Joris1306/Collecteur_de_donnees_animalieres/Stockage_Distant/README/THEME_UPDATE.md

# Login System - Theme Integrated ✅

## What's Changed

✅ **Login Page Updated**
- Now uses your existing `style.css` theme
- Dark background with gradient (matches your design)
- Consistent card styling with glass morphism effect
- Uses all your CSS variables (--text, --muted, --border, etc.)
- Responsive design that works on mobile

✅ **Navbar Example Updated**
- Uses your theme colors and styling
- Consistent with existing design
- Ready to copy-paste into your pages

---

## How It Looks Now

The login page has:
- Your dark blue/green gradient background
- Light text and subtle borders
- Glass morphism cards (matching your design system)
- Consistent button styling
- Same typography and spacing

**Result**: The login page looks like it belongs with your system!

---

## How to Add Navbar to Your Pages

### Simple Option: Copy-Paste

Add this to the top of your existing HTML templates (inside `<body>`):

```html
<nav style="display:flex; justify-content:space-between; align-items:center; padding:16px 20px; border-bottom:1px solid var(--border); background:linear-gradient(180deg, rgba(255,255,255,.05), rgba(255,255,255,.02));">
  <h2 style="margin:0; color:var(--text);">Data Monitoring System</h2>
  <div style="display:flex; gap:20px; align-items:center;">
    <span style="color:var(--muted); font-size:14px;">{{ session.get('user') }}</span>
    <a href="{{ url_for('logout') }}" style="padding:10px 16px; background:linear-gradient(180deg, var(--panel2), var(--panel)); color:var(--text); text-decoration:none; border:1px solid var(--border); border-radius:12px; font-size:14px;">Logout</a>
  </div>
</nav>
```

### Better Option: Use Include

Use the file we created:

```html
{% include 'navbar_example.html' %}
```

Add this to each page, right after `<body>`.

See `templates/navbar_example.html` for the full code.

---

## CSS Variables You Can Use

Your system defines these in `style.css`:

```
--bg          Dark background
--text        Main text (light)
--muted       Secondary text (muted)
--panel       Card/panel background
--panel2      Card variant background
--border      Border color
--shadow      Box shadow
--radius      Border radius (18px)
```

Use them like:
```html
<div style="color: var(--text); border: 1px solid var(--border);">
  Your content
</div>
```

---

## Files Modified/Created

| File | Status | Purpose |
|---|---|---|
| `templates/login.html` | ✅ UPDATED | Now uses style.css theme |
| `templates/navbar_example.html` | ✅ UPDATED | Uses theme colors |
| `THEME_INTEGRATION.md` | ✅ NEW | Integration guide |
| `static/style.css` | ✅ UNCHANGED | Your design system |

---

## Next Steps

1. **Test login page** - Visit `/login`, should match your theme ✓
2. **Test login flow** - Login with admin/admin123 ✓
3. **(Optional) Add navbar to pages** - Copy-paste or use include ✓
4. **(Optional) Create base.html** - For consistent header across all pages ✓

---

## Example: Updating a Page

### Before
```html
<!DOCTYPE html>
<html>
<head>
    <title>My Page</title>
</head>
<body>
    <h1>Content here</h1>
</body>
</html>
```

### After
```html
<!DOCTYPE html>
<html>
<head>
    <title>My Page</title>
    <link rel="stylesheet" href="{{ url_for('static', filename='style.css') }}">
</head>
<body>
    <!-- Add navbar -->
    {% include 'navbar_example.html' %}
    
    <!-- Your content -->
    <h1>Content here</h1>
</body>
</html>
```

---

## Theme Consistency Checklist

- ✅ Login page uses `style.css`
- ✅ Login page matches your design
- ✅ Navbar example created
- ✓ (Optional) Update existing pages with navbar
- ✓ (Optional) Create base.html template
- ✓ (Optional) Ensure all pages link to `style.css`

---

## Summary

Your login system now:
- ✅ **Protects** all web pages with login
- ✅ **Keeps API** endpoints open for devices
- ✅ **Maintains** your design theme throughout
- ✅ **Includes** logout functionality with navbar

Everything is theme-integrated and ready to use!

---

## Support

For more details on:
- **Theme variables**: See `static/style.css`
- **Integration examples**: See `THEME_INTEGRATION.md`
- **Navbar code**: See `templates/navbar_example.html`
- **Login setup**: See `LOGIN_SETUP.md`
