Joris1306/Collecteur_de_donnees_animalieres/Rapport/CDC_PTRANS_CollecteurDonneesAnimalieres.pdf

# Cahier Des Charges

# Nom du projet : Collecteurs de données animalières

Version du document :

Finale

Date du document :

19 / 1 / 2026

Client :

Xavier Leprevost - élu de la mairie de Saint-Mars-du-Désert

Auteurs :

Davy Clark
Ewen Le Callet
Joris Menard
Jules Noumba
Nolan Buchet
Xueying Xu

Janvier 2026

## Table des matières

Page 2 sur 31

## Table des figures

II.1 | Bête à corne | | 7
II.2 | Décomposition en bloc fonctionnel principale | | 8
II.3 | Décomposition en blocs fonctionnels principaux et optionnels | | 9
II.4 | Diagramme des work package principaux (macro) | 10
II.5 | Diagramme Zoom sur le work-package principal numéro 1 "Acquisition des
données ou piège caméra" | 11

II.6 Diagramme Zoom sur le work-package principal numéro 2 "Réception, stockage
et exploitation des données" | 12
VII.1 Gantt des livrables de négociation et de suivi d’avancement du projet | 22

Page 3 sur 31

## Liste des tableaux

I.1 | Informations des intervenants | | 5
I.2 | Informations sur l’équipe de projet | | 6
II.2 | Détection de mouvement animalier | 13
II.4 | Prise de vue automatique | 14
II.6 | Stockage tampon pour transmission vers stockage distant | 15
II.8 | Autonomie énergétique | 16
II.10 Transmission des données | 17
VI.2 Tableau des risques du projet | 21
VIII.2 Signature des parties intervenant dans le projet | 25
XI.4 Comparaison des différentes technologies de transmission possibles | 28
XI.5 Comparaison des modules caméras | 29
XI.6 Comparaison des microcontrôleurs | 30
XI.7 Comparaison des microcontrôleurs (suite) | 31

Page 4 sur 31

# I Retranscription du besoin client

## 1 Contexte

La mairie de Saint-Mars-du-Désert est une collectivité territoriale dynamique et innovante, engagée dans une démarche de transition écologique et sociétale.

Dans ce cadre, la commune souhaite renforcer ses connaissances sur la faune locale en mettant en place un dispositif de surveillance et d’observation automatisée. Ce projet s’inscrit dans une démarche plus large de constitution de l’Atlas de la Biodiversité Communale (ABC), outil essentiel pour inventorier, comprendre et valoriser la richesse écologique du territoire.

Il s’intègre également dans un projet global porté par la municipalité et ses partenaires associatifs, visant au rachat et à la préservation de terrains naturels afin d’en assurer l’étude scientifique, la conservation et la valorisation écologique. Dans ce contexte, le dispositif envisagé pourra constituer un outil d’aide à la décision et un élément de preuve scientifique permettant de documenter la présence et l’évolution des espèces sur ces espaces protégés.

Le système aura pour objectif de capturer des photographies d’espèces animales présentes sur la commune. Dès leur acquisition, ces images seront transmises sans fil à un stockage distant afin d’être analysées par les services municipaux ainsi que par les partenaires scientifiques et associatifs.

## 2 Parties prenantes

Dans le cadre de ce projet, l’entité ayant le rôle de Maîtrise d’ouvrage (MOA)¹
sera la mairie de
Saint-Mars-du-Désert. L’interlocuteur ayant pour objectif de représenter la mairie dans ce projet sera
M. Xavier LEPREVOST, élu à la mairie de Saint-Mars-du-Désert.
QUI | RÔLE | MAIL | MOBILE
LEPREVOST Xavier | Client | Xavier.leprevost@saintmarsdudesert.fr | +33 6 28 34 18 50

Table I.1 – Informations des intervenants

Page 5 sur 31

Un groupe de six étudiants occupera le rôle de Maîtrise d’œuvre (MOE)²
. Ce groupe est composé
de trois étudiants ayant fait un BUT en électronique et informatique, un étudiant ayant fait une prépa PEIP (cursus préparatoire visant à préparer les élèves au cycle ingénieur Polytech), une étudiante ayant fait une licence en génie électrique et un étudiant ayant fait une licence en génie électrique, spécialité AII (automatique et informatique industrielle).
QUI | RÔLE | MAIL | MOBILE
LE CALLET Ewen | Chef de projet | ewen.le-callet@etu.univ-nantes.fr | +33 6 95 15 93 30
NOUMBA Jules | Reponsable work package secondaire Détection mou-vement et capteur T° | jules.noumba@etu.univ-nantes.fr | +33 6 11 83 82 77
BUCHET Nolan | Responsable work package principal Acquisition don-nées ou Piege Camera et du work package secondaire Gestion des échanges don-nées et du microcontrôleur | nolan.buchet@etu.univ-nantes.fr | +33 6 83 68 16 46
XU Xueying | Responsable work package secondaire Module caméra | xueying.xu@etu.univ-nantes.fr | +33 7 82 67 76 72
CLARK Davy | Responsable work package principal Réception, sto-ckage et exploitation des données et du work package secondaire Stockage distant | davy.clark@etu.univ-nates.fr | +33 7 85 78 48 46
MENARD Joris | Responsable work package principal Transmission | joris.menard@etu.univ-nantes.fr | +33 6 71 61 61 96

Table I.2 – Informations sur l’équipe de projet

Le lien avec les partenaires scientifiques, associatifs et naturalistes sera assuré par la mairie, notamment par l’intermédiaire de Xavier Leprevost. Les données et photographies produites dans le cadre du projet seront mises à disposition de la mairie, qui pourra les transmettre aux partenaires concernés et au public selon les besoins.

Page 6 sur 31

# II Besoins fonctionnels

La bête à corne ci-dessous permet de mieux comprendre les fonctions principales du projet, parties prenantes et objectifs du projet.

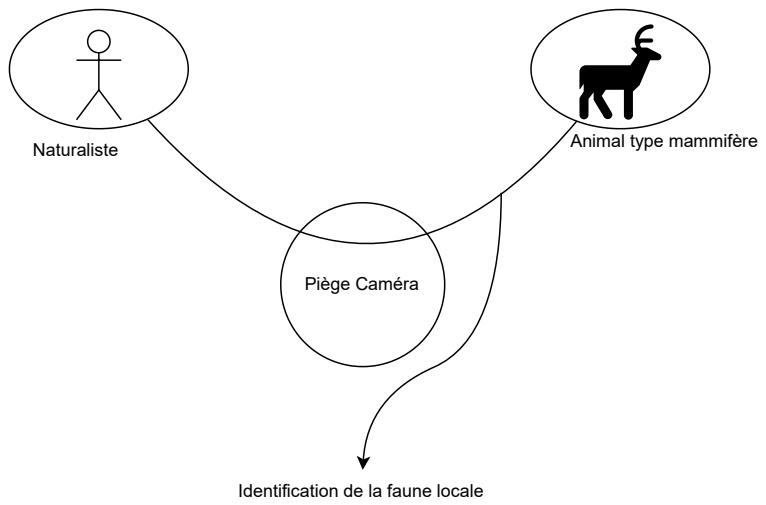
[picture p2: figure]
Piège Caméra; Naturaliste; Animal type mammifère; Identification de la faune locale

Figure II.1 – Bête à corne

Au regard des besoins exprimés par le client, le projet s’inscrit dans une démarche de preuve de concept (POC). L’objectif est de démontrer la faisabilité technique et opérationnelle d’un dispositif simplifié dans des conditions réelles, tout en maîtrisant les coûts et la complexité. Ce choix permet de concentrer les efforts sur un système fonctionnel, d’en valider les principes clés et de poser les bases pour d’éventuelles évolutions futures.

Pour garantir la simplicité et la fiabilité du dispositif, nous proposons de déployer un unique piège caméra, dont la collecte initiale se limitera à la prise de photos, à l’horodatage, la localisation GPS, l’humidité et la température. Cette approche vise à optimiser la gestion énergétique et à réduire la complexité fonctionnelle.

L’architecture du système sera conçue de manière modulaire afin de permettre l’intégration ultérieure d’autres types de données, sans remettre en cause l’ensemble de l’infrastructure.

Les données seront transmises vers un stockage distant dès leur acquisition, sans traitement préalable dans le piège caméra. Cette méthode permet d’éviter les contraintes liées à la gestion d’un stockage local volumineux et à la récupération fréquente des cartes SD, tout en facilitant la logistique et en assurant un accès centralisé aux données.

Enfin, les données seront structurées sous forme tabulaire dans le stockage distant et rendues accessibles via une interface web à accès restreind, afin de faciliter leur consultation, leur exportation et leur exploitation pour l’identification des espèces, conformément aux objectifs du projet.

Page 7 sur 31

Le système d’observation de la faune devra répondre à plusieurs besoins essentiels liés à sa mission principale : la collecte, la transmission et la mise à disposition des données sur les mammifères terrestres locales.

## 1 Fonctionnalités principales

— Détection de mouvement animalier : Le dispositif repose sur la détection automatique de mouvements dans son champ de vision. Il doit cependant être optimisé afin de se déclencher principalement lors de la détection d’un animal.

— Prise de vue automatique : une photo doit être prise dès qu’un mouvement est détecté.

— Enregistrement des images dans une mémoire tampon : les clichés capturés sont enregistrés dans une mémoire locale tampon avec leurs métadonnées (date, heure, température, humidité, position GPS) dans le but d’être transmis par la suite.

— Transmission des données : les données collectées doivent être envoyées vers un stockage distant.

— Autonomie énergétique : le système, basé sur une batterie, doit être capable de fonctionner de manière autonome grâce à une gestion optimisée de la consommation d’énergie. Il devra également intégrer un mécanisme de surveillance permettant de suivre en temps réel la capacité énergétique restante, afin d’anticiper les besoins de recharge ou de maintenance.

— Stockage distant : les données reçues par le piège caméra sont stockées dans un stockage distant dans le but d’être exploités.

— Interface utilisateur Web : une interface simple et ergonomique doit permettre la consultation des données (photos, localisation, informations environnementales, etc ...).

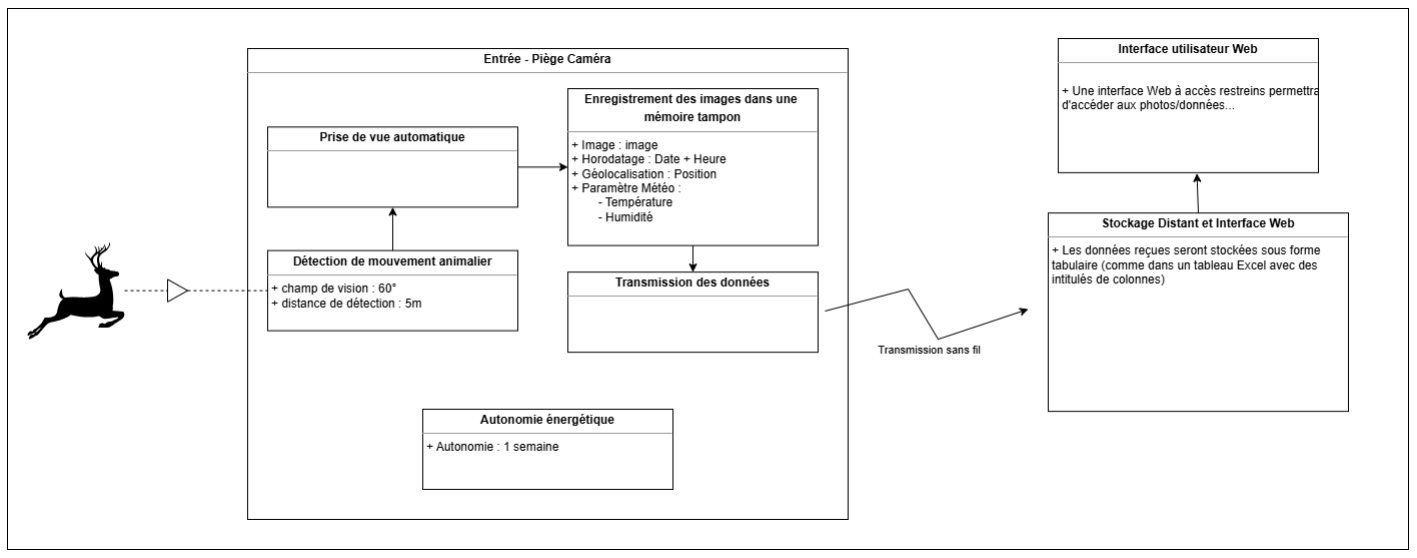
[picture p3: figure]

Figure II.2 – Décomposition en bloc fonctionnel principale

## 2 Fonctionnalités supplémentaires ou optionnelles

— Acquisitions de données environnementales supplémentaires : Ajouts d’autres mesures via divers moyen (pression atmosphérique, CO2, qualité de l’air, son, etc.).

Page 8 sur 31

— Traitement des images par IA : Réaliser une classification animalière sur les images du stockage distant et ajouter le résultat dans la base elle meme. Supression automatique des images non utiles (flous, humains etc...).

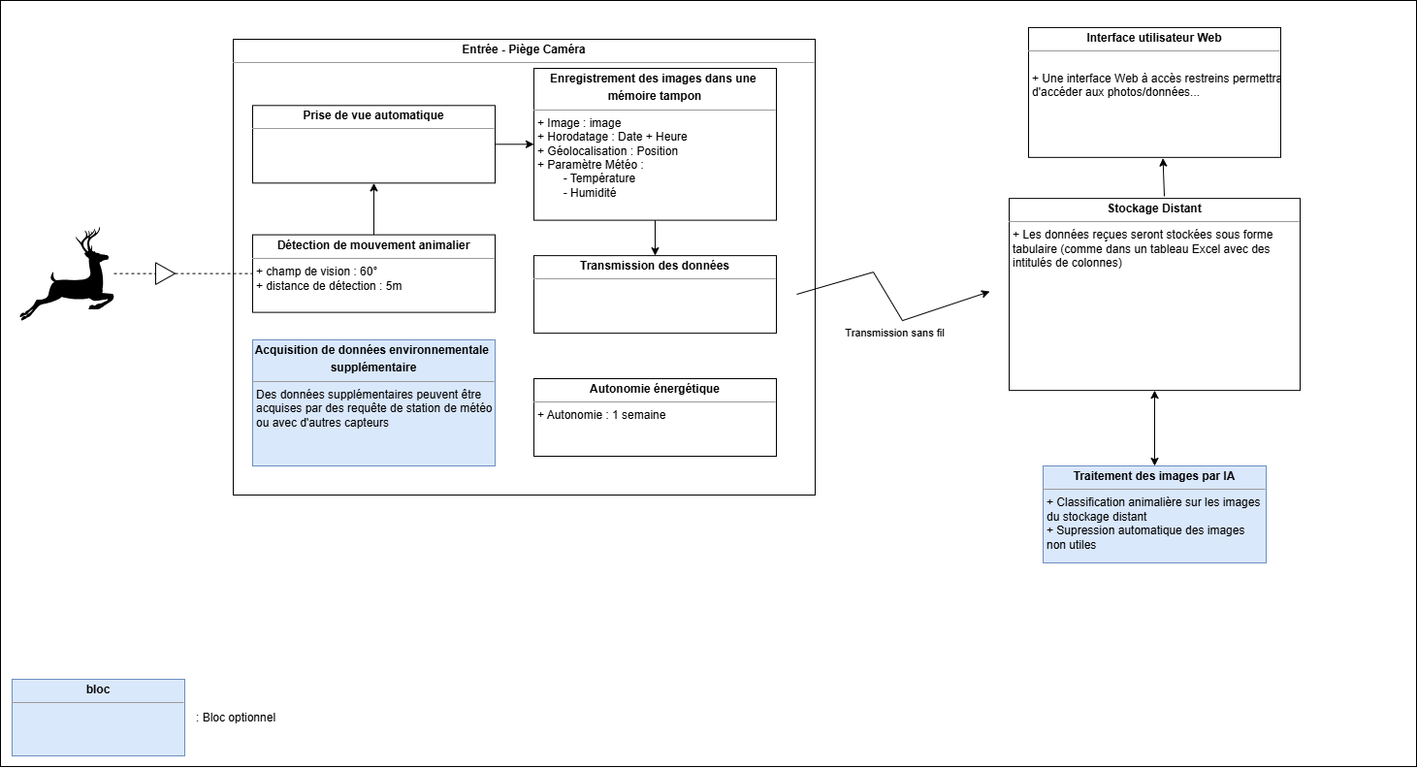
[picture p4: figure]

Figure II.3 – Décomposition en blocs fonctionnels principaux et optionnels

Page 9 sur 31

## 3 Répartition en Work packages

La répartition en WP du point de vu macro se décompose en deux WP principaux (acquisition des données ou piège caméra, puis réception, stockage et exploitation des données) ainsi qu’un WP bis dédié à la transmission. Cette décomposition se justifie par le fait que notre projet peut en réalité être scindé en deux sous-systèmes physiques distincts : le piège caméra et le stockage distant. La transmission constitue ainsi le lien entre ces deux entités.

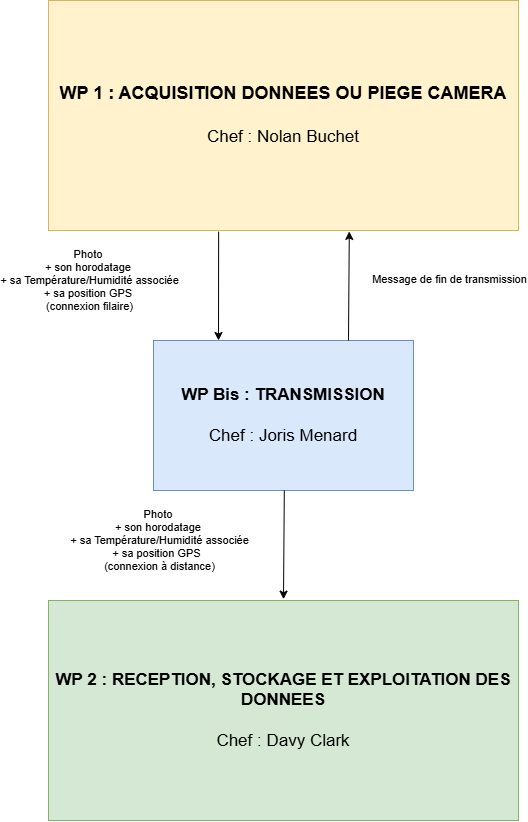
[picture p5: figure]

Figure II.4 – Diagramme des work package principaux (macro)

Décomposons dans un premier temps le WP principal numéro 1, intitulé « Acquisition des données ou piège caméra ». Ce WP est lui-même divisé en trois sous-WP :

— Détection de mouvement et capteurs de température et d’humidité : ce sous-WP a pour objectif le paramétrage du capteur PIR, la compréhension et l’optimisation de la surface de détection permettant le déclenchement des prises de vue. Il assure également l’acquisition des données environnementales associées aux images, à savoir la température et l’humidité.

Page 10 sur 31

— Gestion des échanges de données et du microcontrôleur : ce sous-WP garantit le transfert de l’ensemble des données acquises et la gestion du code embarqué dans le microcontrôleur, qui centralise et coordonne les différentes fonctions du système. Il inclut également la gestion énergétique du dispositif et l’horodatage.

— Caméra : ce sous-WP vise à s’assurer que la caméra réalise des prises de vue de jour comme de nuit avec une qualité suffisante pour l’exploitation des données.

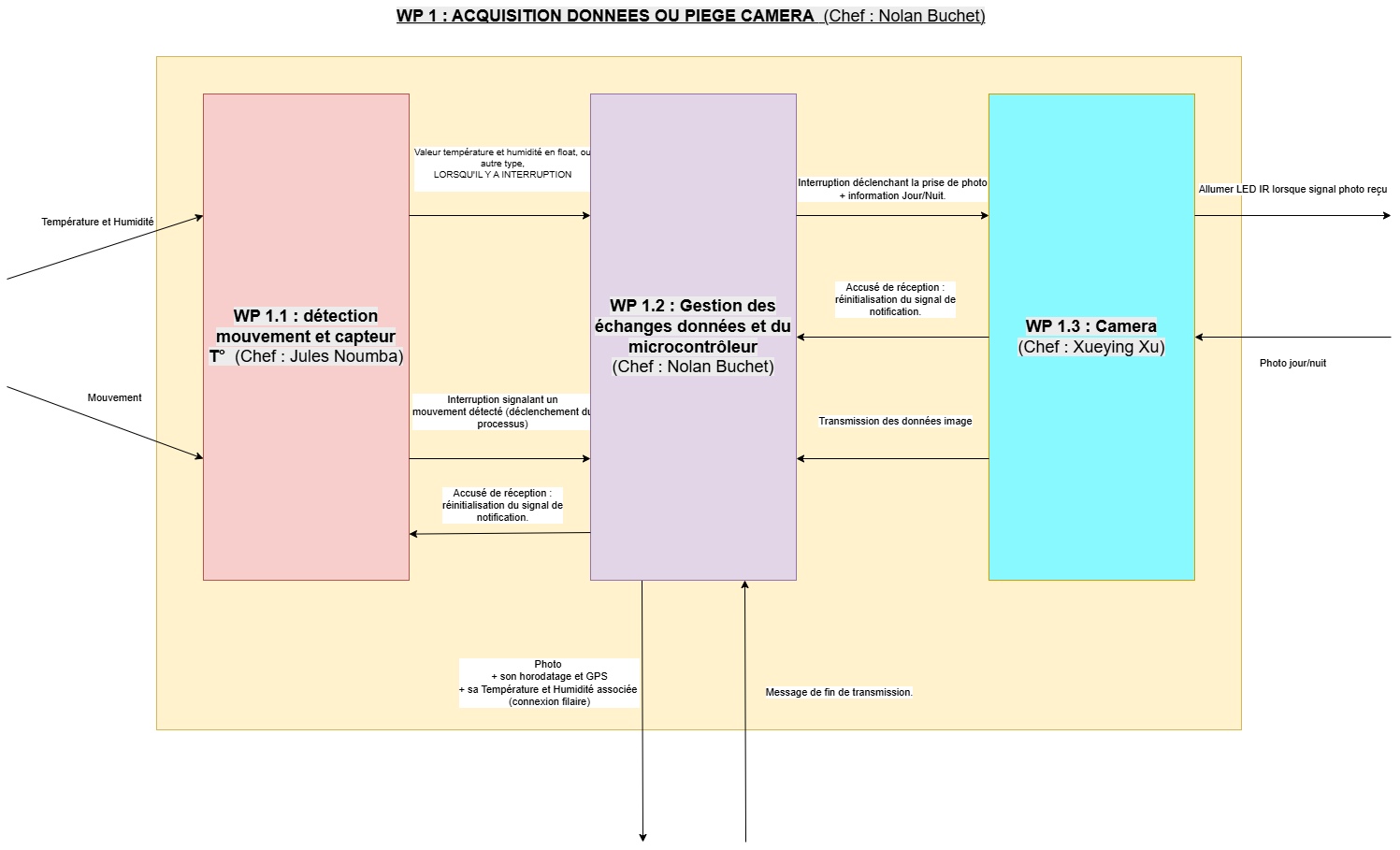
[picture p6: figure]

Figure II.5 – Diagramme Zoom sur le work-package principal numéro 1 "Acquisition des données ou piège caméra"

On se focalise désormais sur le WP principal numéro 2, intitulé « Réception, stockage et exploitation des données ». Ce WP se décompose en un sous-WP principal et deux sous-WP optionnels :

— Stockage distant : ce sous-WP assure la réception des données transmises à distance ainsi que leur stockage sous forme tabulaire sur une infrastructure distante.

— Interface utilisateur Web : ce sous-WP correspond au développement d’une interface web permettant de consulter les images acquises ainsi que les données associées (température, humidité, GPS, etc.). L’accès à cette interface est limité par une authentification.

— Traitement des images par IA – optionnel : ce sous-WP a pour objectif la récupération des images stockées à distance, leur traitement par un algorithme de classification d’animaux basé sur l’intelligence artificielle, puis le renvoi des résultats de la classification vers le stockage distant. On peut également implenter une supression automatique des images du stockage distant en fonction du résultat de l’algorithme IA.

Page 11 sur 31

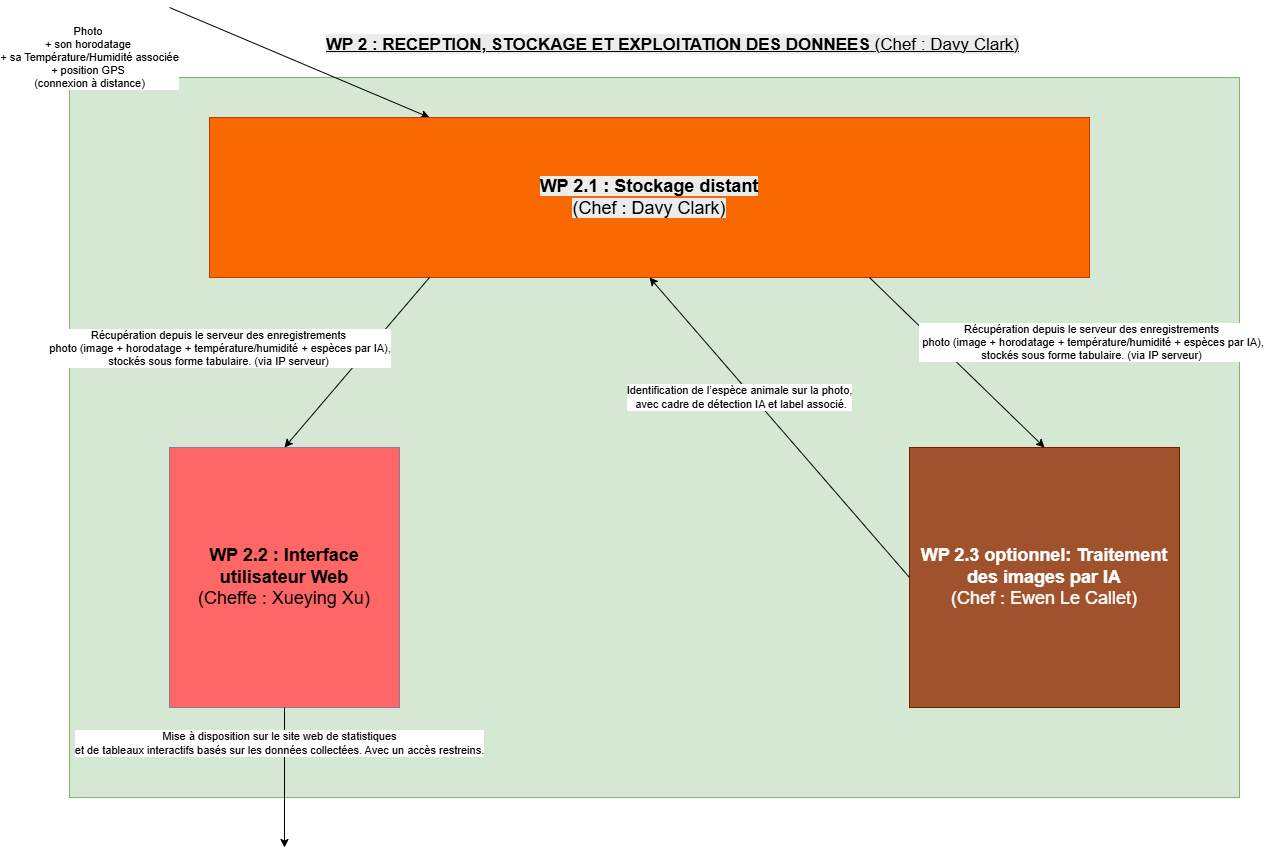
[picture p7: figure]

Figure II.6 – Diagramme Zoom sur le work-package principal numéro 2 "Réception, stockage et exploitation des données"

## 4 Spécifications techniques détaillées

Les tableaux suivants détaillent les spécifications techniques associées à chaque fonctionnalité principale. Pour chaque composant du système, sont précisés les paramètres de performance attendus, les données manipulées et les justifications techniques des choix retenus.

Cette formalisation permet d’établir des critères de validation clairs et d’assurer la cohérence de l’ensemble du système, tout en guidant les choix de conception et la sélection des composants.

Page 12 sur 31

Fonctionnalité | Données | Valeurs nomi-nales | Justification
Détection de présence | Zone de cou-verture | >2 m | Couvre la distance réaliste pour la plupart des animaux ciblés tout en limitant les déclenche-ments lointains dus au vent, branches ou objets ambiants ; réduit la consommation
| Angle de dé-tection | > 80 ° | Un angle minimal (>20°) ga-rantit qu’un animal traversant le champ proche est détecté sans multiplier les faux posi-tifs provoqués par une ouver-ture trop large.
Sensibilité du capteur | Temps de ré-action | ď 1 s après détection | Permet d’assurer la prise de vue de l’animal avant qu’il ne quitte la zone ; on peut viser ď1 s si le matériel et l’alimentation le permettent.
Adaptation environnementale | Conditions de fonctionne-ment | Jour / Nuit / Toutes saisons | mode jour et nuit, pour assurer couverture continue de la zone étudiée.
Température | Température de fonction-nement | -20 °C à +50 °C | Plage suffisante pour la majo-rité des zones tempérées ; pro-tège composants et batterie contre températures extrême
Etanchéité | | IP66 | Assure une protection totale contre la poussière et les pro-jections d’eau, adaptée à une installation extérieure perma-nente.

Table II.2 – Détection de mouvement animalier

Page 13 sur 31

Fonctionnalité | Données | Valeur No-minale | Justification
Distance | Portée maxi-male de photo exploitable | < 5 m | Une portée inférieure à 5 m permet de ga-rantir une bonne qualité d’image et une dé-tection efficace des animaux proches,
Champs | Champ de vi-sion de la ca-méra | > 20 ° | Un angle minimal (>20°) garantit qu’un animal traversant le champ proche est dé-tecté sans multiplier les faux positifs provo-qués par une ouverture trop large.
Enregistrement de l’image | Qualité de l’images | > 480p | Une résolution supérieure à 480p garantit une identification correcte des espèces tout en limitant la taille des fichiers pour un sto-ckage local efficace.
Nocturne | Prise de photo la nuit | Oui | La capture nocturne est indispensable pour un piège caméra, car de nombreuses espèces sont actives la nuit
Température | Témperature de fonction-nement | -15 °C / +50 °C | Plage suffisante pour la majorité des zones tempérées ; protège composants et batterie contre températures extrême
Rotation | Rotation de la caméra | Non | L’absence de rotation réduit la consomma-tion énergétique, le coût du dispositif et la complexité mécanique, tout en suffisant pour une zone de surveillance fixe.
Connectivité | Type de connectivité | Filaire | Une connexion filaire de la caméra sur le mi-crocontrolleur garantit la fiabilité du trans-fert.
Etanchéité | Norme Elec-tronique | IP66 | Assure une protection totale contre la pous-sière et les projections d’eau, adaptée à une installation extérieure permanente.
Type de flux | Flux interne | Photo | Le mode photo est prioritaire pour minimi-ser l’énergie consommée et maximiser la du-rée d’autonomie
Capture d’image | Format | JPEG/PNG | Ces formats standards assurent une compa-tibilité universelle et une bonne compression sans perte excessive de qualité.

Table II.4 – Prise de vue automatique

Page 14 sur 31

Fonctionnalité | Données | Valeurs nomi-nales | Justification
Enregistrement local tampon | Support de stockage | Mémoire interne (microSD 32 Go min.) | Une carte microSD est peu coûteuse, facilement remplaçable et offre une ca-pacité suffisante pour stocker plusieurs jours.
Sauvegarde auto-matique | Fréquence d’enregistre-ment | À chaque détection de mouvement | Cette logique d’enregistrement ga-rantit qu’aucun événement anima-lier n’est perdu tout en limitant la consommation mémoire.
Métadonnées as-sociées | Date et heure d’ac-quisition | Format ISO 8601 (AAAA-MM-JJ HH :MM :SS) | Le format ISO standardise les enregis-trements temporels, facilitant la syn-chronisation et le tri automatisé des fichiers.
| Température ambiante | ±1 °C de précision | précision suffisante pour les besoins terrain.
| Position GPS | Précision ď 5 m | Une précision inférieure à 5 m est suf-fisante pour localiser précisément la zone de capture
Gestion mémoire | Seuil d’alerte de satura-tion | 90 % d’utilisation de la capacité | Définir une alerte avant saturation permet d’éviter la perte de données
Effacement auto-matique | Politique de remplace-ment | Suppression des plus anciens fichiers lorsque transmis-sion effectuée | Assure la continuité du stockage sans intervention humaine

Table II.6 – Stockage tampon pour transmission vers stockage distant

Page 15 sur 31

Fonctionnalité | Données | Valeurs nominales | Justification
Source | Type de bat-terie | Li-ION | Les batteries Li-Ion offrent une haute densité énergétique, une bonne durée de vie, et sont facilement rechargeables, ce qui les rend idéales pour un dispositif autonome en extérieur.
Tension | | 3.7V | Tension standard pour les modules électro-niques basse consommation, assurant compa-tibilité avec la plupart des composants embar-qués.
Autonomie | Duré de fonctionne-ment | 1 semaine | Une autonomie d’une semaine garantit un fonctionnement prolongé sans intervention hu-maine
Gestion Energé-tique | Mode de veille | 30 s de dé-tections | Permet de réduire significativement la consom-mation lorsque le dispositif est inactif, tout en maintenant une réactivité satisfaisante à la dé-tection suivante.
Conso veille | | < 100 uA | Très faible consommation permettant d’écono-miser la batterie sur les longues périodes d’in-activité, essentielle pour un piège caméra sou-vent en veille.
Conso Activité | | < 1 W | Une faible consommation en activité prolonge la durée de fonctionnement global et limite les besoins de recharge fréquente.
Protection elec-trique | Sécurité | Surchage | La protection contre la surcharge empêche toute détérioration de la batterie lors de la re-charge, augmentant la sécurité et la durée de vie du système.
| Surtension | | La protection contre la surtension protège les circuits électroniques contre les variations de tension, garantissant la fiabilité du dispositif.
Information | | Envoie une alerte concernant < 10 % | Une alerte de batterie faible permet d’anticiper la recharge ou le remplacement avant l’arrêt complet du système, évitant la perte de don-nées ou d’observations.
Plage de fonc-tionnement | Température de fonction-nement | -20 °C à +50 °C | Assure la fiabilité du système dans la plu-part des environnements naturels, incluant des conditions hivernales et estivales extrêmes.

Table II.8 – Autonomie énergétique

Page 16 sur 31

Fonctionnalité | Données | Valeurs no-minales | Justification
Type de commu-nication | 4G | Sans Fils | La communication sans fil permet un transfert automatique des données sans in-tervention manuelle, indispensable pour un système autonome déployé sur le terrain.
Donnée | | Image
| | Metadonnées
Stockage distant | Type de ser-veur | Serveur local | Un serveur local permet une liberté suffi-sante pour répondre de plusieurs manières différentes aux besoins.
Consomation | Mode de trans-mission | < 2 W | La consommation limitée à 2 W préserve l’autonomie énergétique du système lors des envois, particulièrement importants si la transmission est fréquente.
Condition d’en-voie | Declanchement | Envoie après Chaque cap-ture | L’envoi immédiat permet la mise à jour en temps réel des données dans le stockage distant, utile pour un suivi continu ou des alertes rapides.

Table II.10 – Transmission des données

Page 17 sur 31

# III Besoins non fonctionnels

En plus des fonctionnalités attendues, le système devra respecter plusieurs contraintes techniques et qualitatives :

— Fiabilité : le système doit fonctionner de manière continue dans des conditions extérieures variables (pluie, vent, variations de température).

— Robustesse : les composants matériels doivent être les plus résistants possibles aux intempéries et aux chocs.
— Évolutivité : l’architecture logicielle et matérielle doit permettre l’ajout de nouveaux capteurs ou modules sans modification majeure.

— Performance : la détection et la transmission doivent être sans perte d’informations.

— Energie et autonomie : Comme on peut le constater dans le tableau des spécifications cidessus, le système doit être conçu pour une faible consommation énergétique et disposer d’une autonomie suffisante afin d’assurer un fonctionnement prolongé. Une autonomie de 1 semaine a été définie afin de garantir la flexibilité du système et d’assurer sa continuité de fonctionnement.

Page 18 sur 31

# IV Évolution potentielle des besoins

Le système devra être conçu pour permettre des évolutions futures, tant sur le plan matériel que logiciel :

— Amélioration du traitement d’image : intégration d’algorithmes plus performants de reconnaissance d’espèces animales à l’aide de l’intelligence artificielle.

— Ouverture vers la participation citoyenne : intégration complète d’une application mobile et mise en place d’un système de validation des données saisies par les habitants.

— Interopérabilité : possibilité de connecter le système à d’autres bases de données environnementales régionales ou nationales.

— Extension du réseau de surveillance : déploiement de plusieurs caméras réparties sur un vaste périmètre afin d’assurer une couverture complète de la zone. Les données sont d’abord centralisées localement via un module de regroupement chargé de collecter les données des différentes caméras, puis transmises vers le serveur central.

Page 19 sur 31

# V Limites du projet

Ce projet vise exclusivement la prise d’informations (photo, GPS, horodatage, température, humidité) liés à l’identification d’animaux terrestres de taille significative (ex. mammifères sauvages). Afin d’assurer un cadrage clair du besoin, les limites suivantes sont définies

## 1 Fonctionnalités limitées à la détection et de la prise de vue

Bien que le système, basé sur la détection de mouvement, puisse être parasité par la détection d’humains, d’oiseaux ou d’autres éléments, son objectif principal reste la détection et la photographie d’animaux terrestres. Les insectes, oiseaux, petits rongeurs et tout animal de taille trop réduite ne sont pas pris en compte dans le cadre du projet. Le système ne réalise aucune capture vidéo, seules des photographies sont enregistrées par la caméra. Le projet se limite à un but d’identification d’espèces et non d’analyse du comportement.

## 2 Couverture géographique restreinte

Les tests et le déploiement initial sont réalisés exclusivement sur le territoire de Saint-Mars-du-Désert, dans le bois communal.

## 3 Conditions d’installation contrôlées

Le dispositif est destiné à être fixé sur un support solide (arbre, poteau, structure dédiée). Aucune installation dans l’eau ou dans des sols boueux instables n’est envisagée.

Page 20 sur 31

# VI Risques

Cette section présente les risques identifiés pour le projet, classés par catégorie. Pour chaque risque, nous indiquons la probabilité d’occurrence, la gravité et le niveau de risque, ainsi que les mesures préventives ou correctives proposées. L’objectif est d’anticiper les incidents potentiels et de définir des actions permettant de réduire leur impact sur le planning, le budget et la qualité des livrables.

Catégorie | Risque identifié | Probabilité | Gravité | Niveau de risque | Mesures pré-ventives / Correctives
Gestion de projet | Mauvaise réparti-tion des tâches | moyen | moyen | moyen | Fiche de suivi des tâches
Gestion de projet | Mauvaise com-munication avec le client | moyen | haut | haut | Communiquer régulièrement et précisément avec le client
Gestion de projet | Mauvaise com-munication entre les membres | faible | haut | moyen | Team building, baromètre d’at-mosphère de l’équipe
Gestion de projet | Prise de décisions | moyen | moyen | moyen | Répartition en Work Package Work Package (WP)³
Gestion de projet | Mécompréhension due à la barrière de la langue | moyen | moyen | moyen | Nommer per-sonnes chargées de la traduction et former duo
Gestion de projet | Manque d’impli-cation dû à la lar-geur du groupe | haut | moyen | moyen | Donner des tâches per-sonnalisés et responsabiliser l’équipe

Table VI.2 – Tableau des risques du projet

Page 21 sur 31

# VII Planning

Durant ce projet, plusieurs types de livrables seront remis au client, tel que les comptes-rendus de réunion, les soutenances, ou d’autres documents de suivi. Afin de clarifier certains points d’interrogation et de rendre compte de l’avancement du projet. Par ailleurs, il existe également les livrables produits, qui correspondent aux différentes composantes du produit à rendre tout au long de la phase de développement, ou au produit final lui-même à rendre à la fin du projet.

Le diagramme de Gantt ci-dessous permet de visualiser les livrables, tels que les réunions et les documents à remettre au client.

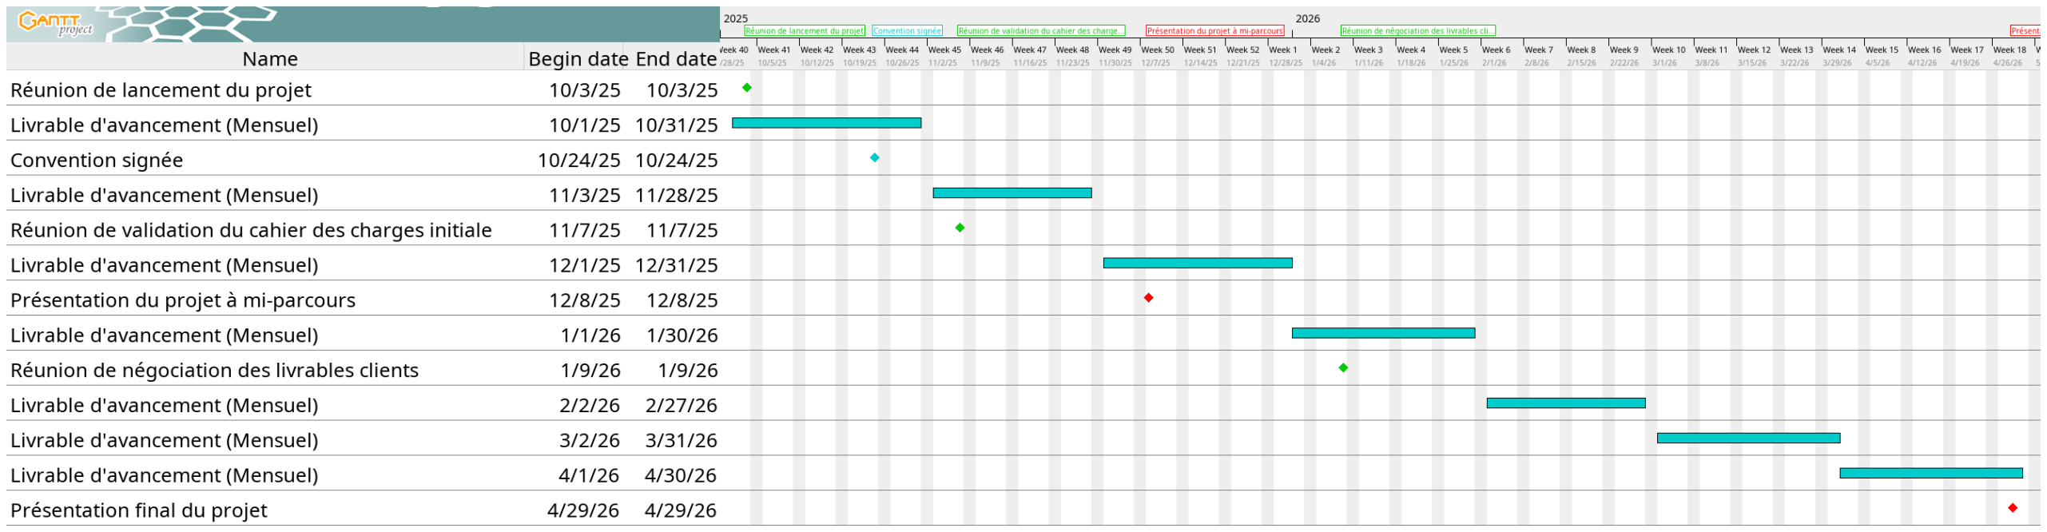
[picture p8: figure]

Figure VII.1 – Gantt des livrables de négociation et de suivi d’avancement du projet

Un court rapport mensuel sera remis au client afin de suivre l’avancement du projet. La fréquence de remise de ce rapport pourra évoluer au cours du projet selon les demandes du client.

Page 22 sur 31

# VIII Gestion de projet

## 1 Décomposition en work packages (WP)

Le projet est structuré en différents WP, permettant une répartition claire et cohérente des tâches entre les membres de l’équipe. Cette organisation facilite la gestion du projet, la responsabilisation de chaque collaborateur et le suivi de l’avancement des travaux.
D’un point de vue macro, le projet est décomposé en deux WP principaux et un WP bis. Cette décomposition repose sur l’architecture globale du système, qui peut être scindée en deux sous-systèmes physiques distincts : le piège caméra et le stockage distant. Le WP bis « Transmission » assure le lien fonctionnel entre ces deux entités.

### 1.1 Work packages principaux

WP1 – Acquisition des données ou piège caméra Ce WP regroupe l’ensemble des fonctionnalités liées au sous-système embarqué. Il comprend notamment l’acquisition des images et des données environnementales, ainsi que la gestion du matériel et de l’énergie. Il se décompose en plusieurs sous-WP :
— Détection de mouvement et capteurs environnementaux : paramétrage du capteur PIR, optimisation de la zone de détection et acquisition des données de température, d’humidité et autres métadonnées associées aux images.
— Gestion des échanges de données et du microcontrôleur : centralisation des données, gestion du code embarqué, horodatage et gestion énergétique du dispositif.
— Caméra : sélection et intégration du module caméra afin d’assurer des prises de vue de jour comme de nuit avec une qualité suffisante pour l’exploitation des données.

WP2 – Réception, stockage et exploitation des données Ce WP concerne le sous-système distant et le traitement des données transmises par le piège caméra. Il se décompose en 2 sous-WP principaux et un sous-WP optionnel :

— Stockage distant : ce sous-WP assure la réception des données transmises à distance ainsi que leur stockage structuré sous forme tabulaire sur une infrastructure distante.
— Interface utilisateur Web : ce sous-WP correspond au développement d’une interface web permettant de consulter les images acquises ainsi que les données associées (température, humidité, coordonnées GPS, etc.). L’accès à cette interface est limité par un mécanisme d’authentification afin de garantir la confidentialité des données.
— Traitement des images par IA – optionnel : ce sous-WP a pour objectif la récupération des images stockées à distance, leur traitement par un algorithme de classification d’animaux basé sur l’intelligence artificielle, puis le renvoi des résultats de la classification vers le stockage distant. Il pourra également intégrer une suppression automatique des images du stockage distant en fonction des résultats fournis par l’algorithme d’IA.

### 1.2 Work package bis – Transmission

Le WP bis « Transmission » est transverse aux deux WP principaux. Il a pour objectif d’assurer la communication sans fil entre le piège caméra et le stockage distant. Ce WP inclut le choix de la

Page 23 sur 31 technologie de communication, la fiabilité des échanges et la validation de la trame de données, ainsi que l’optimisation de la consommation énergétique liée à la transmission.

Page 24 sur 31

## 2 Signatures du projet

Date | et | signature | du
client

Date et signature du chef
de projet
Date | et | signature | des
coachs de projet

Table VIII.2 – Signature des parties intervenant dans le projet

Page 25 sur 31

# IX Démarche de transition écologique

Ce projet s’inscrit pleinement dans une démarche de transition écologique en soutenant la connaissance et la préservation de la biodiversité locale. Ce projet facilite la collecte d’images d’animaux sauvages pour alimenter l’atlas de la biodiversité communale et aider les experts à mieux inventorier la faune du territoire.

Page 26 sur 31

Page 27 sur 31

# XI Annexes

Afin de trouver la meilleur solution technique pour chaque work package du projet, un Benchmark⁴ à été mis en place dans lequel les composants ou différentes solutions sont comparées selon différents critères.

Mode Principe Portée

typique

Débit

indicatif

Avantages Inconvénients Coût /

régulation

Cas

d’usage

### Énergie Prix

Transmission

HF

(modulation

FM)

Radio HF

(3–30 MHz)

avec

modulation

FM

Locale à

mondiale
selon

antenne

kb/s à

dizaines

kb/s

Très

grande

portée,

robuste

Débit limité,
antennes

encombrantes

Autorisation
si > 5 W

Télécom
longue

distance,
backup

5 W 25

€

LoRa Modulation

chirp

(LPWAN)

0.5–15 km

selon envi-

ronnement

0.3 – 50

kb/s

Faible

consommation,
grande
portée

Débit limité,
duty-cycle

Faible coût,
pas d’abon-

nement

IoT

capteurs,

télémétrie

0,2 W 30

€

4G (LTE) Réseau

cellulaire

Couverture
nationa-

le/internationale

1–100+
Mb/s

Haut

débit,

mobilité,
bonne

latence

Payant (SIM),
énergivore

Abonnement,

licences

Vidéo,

cloud, gros
volumes

2 W 70

€

Réseau cartes
(filaire/sans

fil)

SPI/I2C/

RS485/BLE/

Zigbee

„5–10 m
(selon

solution)

Centaines
kb/s à

plusieurs
Mb/s

Simple,
faible

latence,
économique

Portée limitée,
dépend du
protocole

Faible coût Robotique,
modules
locaux

0,1 W Dépend

du

µ

C

Wi-Fi HaLow
(802.11ah)

Wi-Fi

sub-GHz pour

IoT

Jusqu’à

plusieurs

centaines

de mètres

kb/s à

centaines

kb/s

Longue
portée

Wi-Fi,

bonne pénétration

Peu répandu,

matériel

spécifique

Puces

dédiées, ISM

IoT longue
portée,

réseaux

capteurs

0,7 W 30

€

ESP-NOW Proto.

Espressif communication

directe Wi-Fi

50–100 m
(urbain),

200–250 m
(champ)

„1–2

Mb/s

(pratique

<1 Mb/s)

Faible

latence,
pas de

routeur,
facile

Limité aux

ESP, pas de

routage, portée

< LoRa

Très faible

coût (ESP32

< 5

€)

Communi-

cation
ESP

(robots,

IoT local)

1,5 W 10

€

Table XI.4 – Comparaison des différentes technologies de transmission possibles

Page 28 sur 31

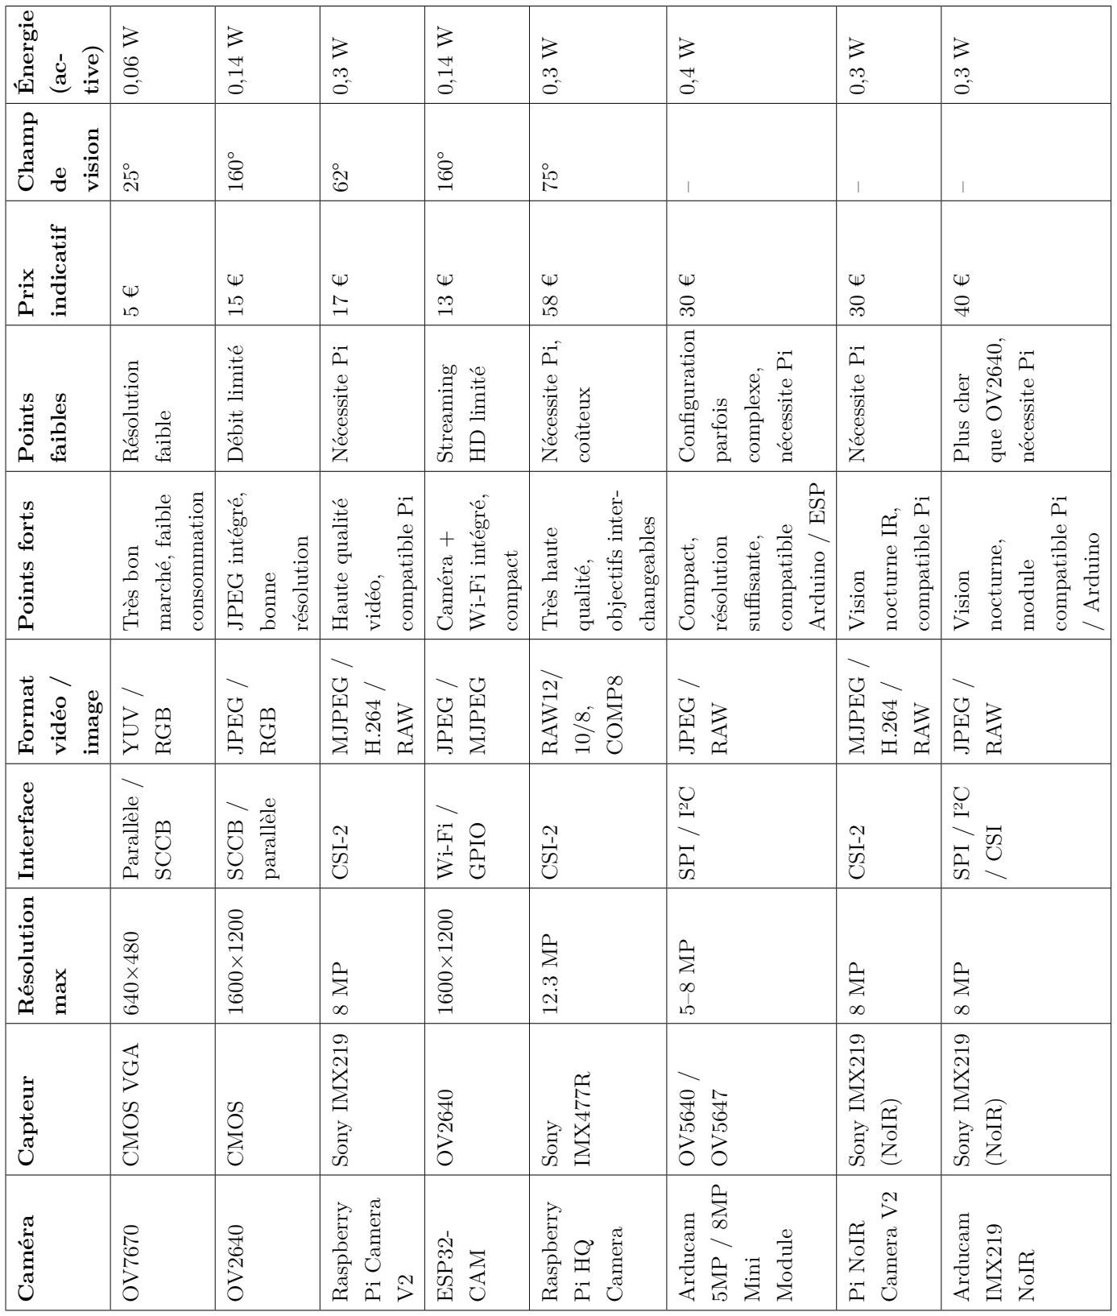
[picture p9: figure]
Caméra Capteur Résolution; max; Interface Format; vidéo /; image; Points forts Points; faibles; Prix; indicatif; Champ; vision; Énergie; tive); OV7670 CMOS VGA 640; ×480 Parallèle /; SCCB; YUV /; RGB; Très bon; marché, faible; consommation; Résolution; faible; OV2640 CMOS 1600; ×1200 SCCB /; parallèle; JPEG /; JPEG intégré,; bonne; résolution; Débit limité 15; Raspberry; Pi Camera; Sony IMX219 8 MP CSI-2 MJPEG /; RAW; Haute qualité; vidéo,; compatible Pi; Nécessite Pi 17; ESP32-; CAM; GPIO; MJPEG; Caméra +; Wi-Fi intégré,; compact; Streaming; HD limité; Camera; Sony; IMX477R; 12.3 MP CSI-2 RAW12/; COMP8; Très haute; qualité,; objectifs inter-; changeables; Nécessite Pi,; coûteux; Arducam; Mini; Module; 5–8 MP SPI / I2C JPEG /; Compact,; suffisante,; compatible; Arduino / ESP; Configuration; parfois; complexe,; nécessite Pi; Pi NoIR; Camera V2; Sony IMX219; (NoIR); 8 MP CSI-2 MJPEG /; Vision; nocturne IR,; Nécessite Pi 30; IMX219; NoIR; 8 MP SPI / I2C; / CSI; nocturne,; module; / Arduino; Plus cher; que OV2640,

Table XI.5 – Comparaison des modules caméras

Page 29 sur 31

Microcontrôleur

/ Carte

Processeur Fréquence RAM Flash Connectivité GPIO / I/O Points forts Points faibles Prix in-

# dicatif Puissance

Arduino Uno (AT-

mega328P) AVR 8-bit 16 MHz 2 KB 32 KB USB / UART 14 digital / 6 analog Très simple, stable, énorme
support commu-

nauté

Faible puissance,
mémoire limitée

20

€ 0.30 W

Arduino Nano 33

BLE

ARM Cortex-

# M4 64 MHz 32 KB 256 KB BLE 14 digital / 8 analog BLE intégré, faible consom-

# mation, compact Plus cher que Nano classique 22.5

€ 0.035 W

Arduino Mega 2560 AVR 8-bit 16 MHz 8 KB 256 KB USB / UART 54 digital / 16

analog

Beaucoup de
GPIO, support

shield

Lent, mémoire
RAM limitée

25

€ 0.357 W

SAMD21 ARM Cortex-

M0+ 48 MHz 32 KB 256 KB USB / UART 14 digital / 6 analog Faible consom- mation, 32-bit Moins répandu que Uno 20

€ 0.025 W

STM32F103C8

(Blue Pill)

ARM Cortex-

M3 72 MHz 20 KB 64 KB USB / UART / SPI / I2C 37 digital / 10 analog Puissant, rapide, compact, pas

cher

Écosystème

moins simple

que Arduino

5 € 0.01 W

Table XI.6 – Comparaison des microcontrôleurs

Page 30 sur 31

Microcontrôleur

/ Carte

Processeur Fréquence RAM Flash Connectivité GPIO / I/O Points forts Points faibles Prix in-

# dicatif Puissance

ESP8266 Tensilica 32-

bit

80–160
MHz

160
KB

4 MB Wi-Fi 17 digital / 1

analog

Wi-Fi intégré, petit, bon

marché

Moins de GPIO,

pas BLE

4 € 0.4 W

ESP32 Tensilica

Xtensa dualcore 32-bit

240 MHz 520
KB

4 MB Wi-Fi + BLE 34 digital / 18

analog

Wi-Fi + BLE in-

# tégré, puissant Plus complexe à programmer

que Arduino

classique

8 € 0.7 W

ESP32-CAM Tensilica

Xtensa 32-bit

240 MHz 520
KB

4 MB Wi-Fi + BLE Caméra +

GPIO

Caméra + Wi-Fi
intégré, compact

Pas facile pour

debugging,

consommation
plus élevée

9.5

€ 1.25 W

Raspberry Pi 4 ARM Cortex-

A72 quad-

core 1.5 GHz 2–8 GB SDCard Ethernet, Wi- Fi, BLE GPIO 40 broches Puissant, Linux, multi-tâches, HDMI, USB Consommation élevée, pas mi- crocontrôleur

pur

55

€ 4 W

Raspberry Pi Zero ARM1176JZF-

S 1 GHz 512 MB SDCard Wi-Fi / BLE (Zero W) GPIO 40 broches Petit, faible coût, Linux Faible puissance CPU, Linux

obligatoire

12.5

€ 0.7 W

Raspberry Pi Pico RP2040 dual-

core ARM
Cortex-M0+

133 MHz 264
KB

2 MB USB 26 digital / 3

analog

Très bon compromis prix/-

puissance,

RP2040 pro-

grammable C /
MicroPython

Pas de Wi-Fi na-

tif

5 € 0.135 W

Table XI.7 – Comparaison des microcontrôleurs (suite)

Page 31 sur 31
