Joris1306/Collecteur_de_donnees_animalieres/Stockage_Distant/DOCUMENT/rapport_documention/images/diagramme_wp+fp.pdf

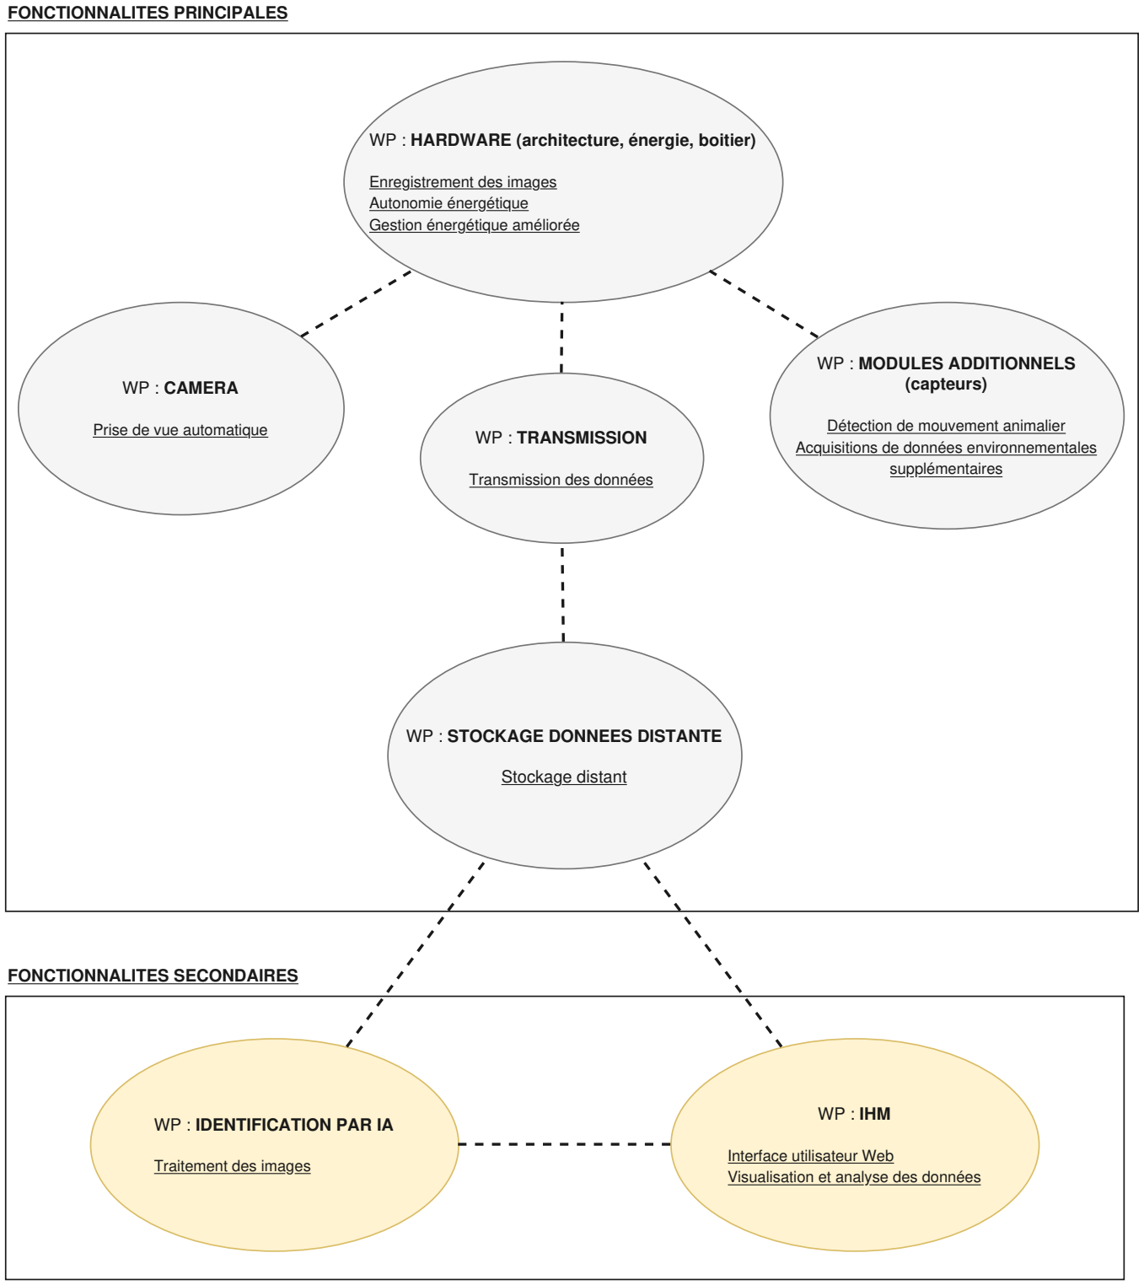
[picture p114: figure]
WP : TRANSMISSION; Transmission des données; WP : CAMERA; Prise de vue automatique; Enregistrement des images Autonomie énergétique Gestion énergétique améliorée; WP : MODULES ADDITIONNELS (capteurs); Détection de mouvement animalier Acquisitions de données environnementales supplémentaires; WP : STOCKAGE DONNEES DISTANTE; Stockage distant; FONCTIONNALITES PRINCIPALES; FONCTIONNALITES SECONDAIRES; WP : IDENTIFICATION PAR IA; Traitement des images; WP : IHM; Interface utilisateur Web Visualisation et analyse des données

WP : HARDWARE (architecture, énergie, boitier)
