Joris1306/Collecteur_de_donnees_animalieres/Stockage_Distant/DOCUMENT/rapport_documention/images/wp_diagramme.pdf

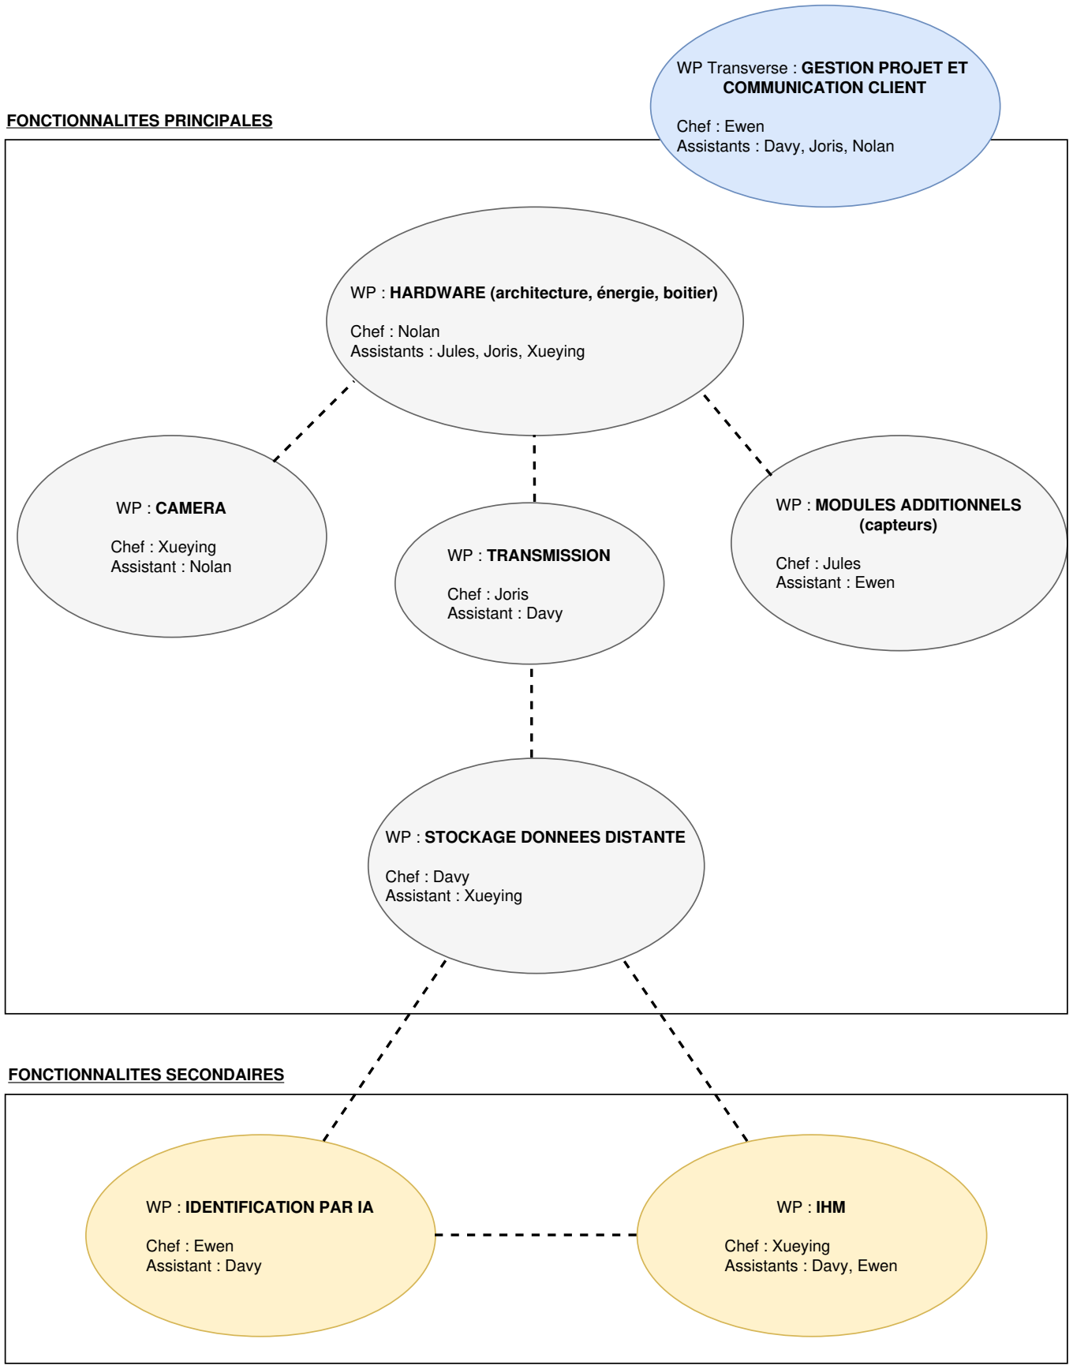
[picture p115: figure]
WP : TRANSMISSION; Chef : Joris Assistant : Davy; WP : CAMERA; Chef : Xueying Assistant : Nolan; Chef : Nolan Assistants : Jules, Joris, Xueying; WP : MODULES ADDITIONNELS (capteurs); Chef : Jules Assistant : Ewen; WP : STOCKAGE DONNEES DISTANTE; Chef : Davy Assistant : Xueying; FONCTIONNALITES PRINCIPALES; WP Transverse : GESTION PROJET ET COMMUNICATION CLIENT; Chef : Ewen Assistants : Davy, Joris, Nolan; FONCTIONNALITES SECONDAIRES; WP : IDENTIFICATION PAR IA; Chef : Ewen Assistant : Davy; WP : IHM; Chef : Xueying Assistants : Davy, Ewen

WP : HARDWARE (architecture, énergie, boitier)
