Joris1306/Collecteur_de_donnees_animalieres/Stockage_Distant/SRC/filtrage_flou/IMG_6897.png

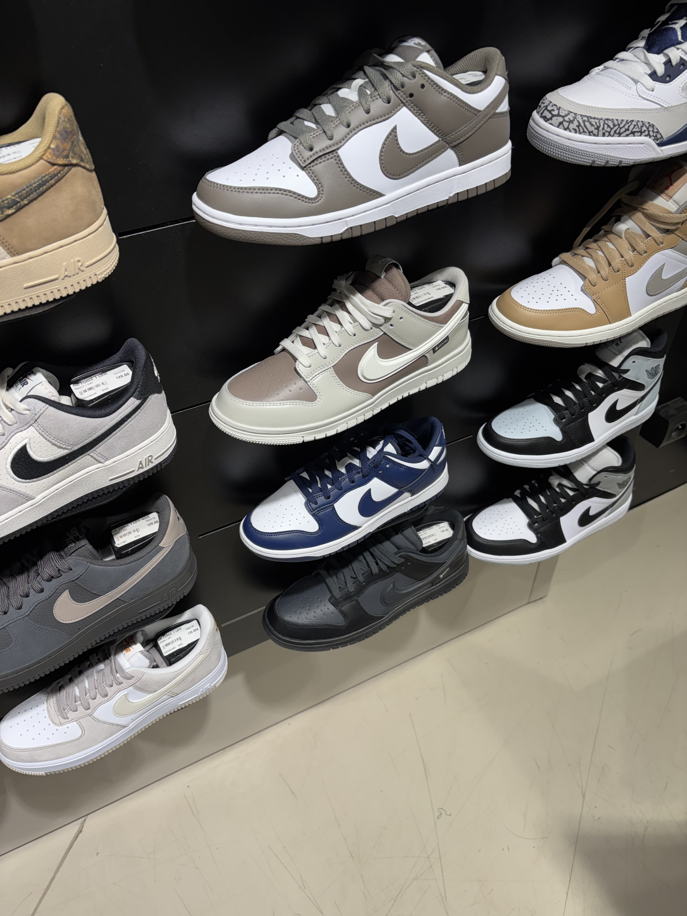
Stockage_Distant/SRC/filtrage_flou/IMG_6897.png
