Joris1306/Collecteur_de_donnees_animalieres/ESP32_TEST/image_reconstruite.png

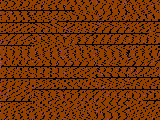
ESP32_TEST/image_reconstruite.png
