Joris1306/Collecteur_de_donnees_animalieres/Stockage_Distant/DOCUMENT/rapport_documention/images/schema_fontionnel_global.pdf

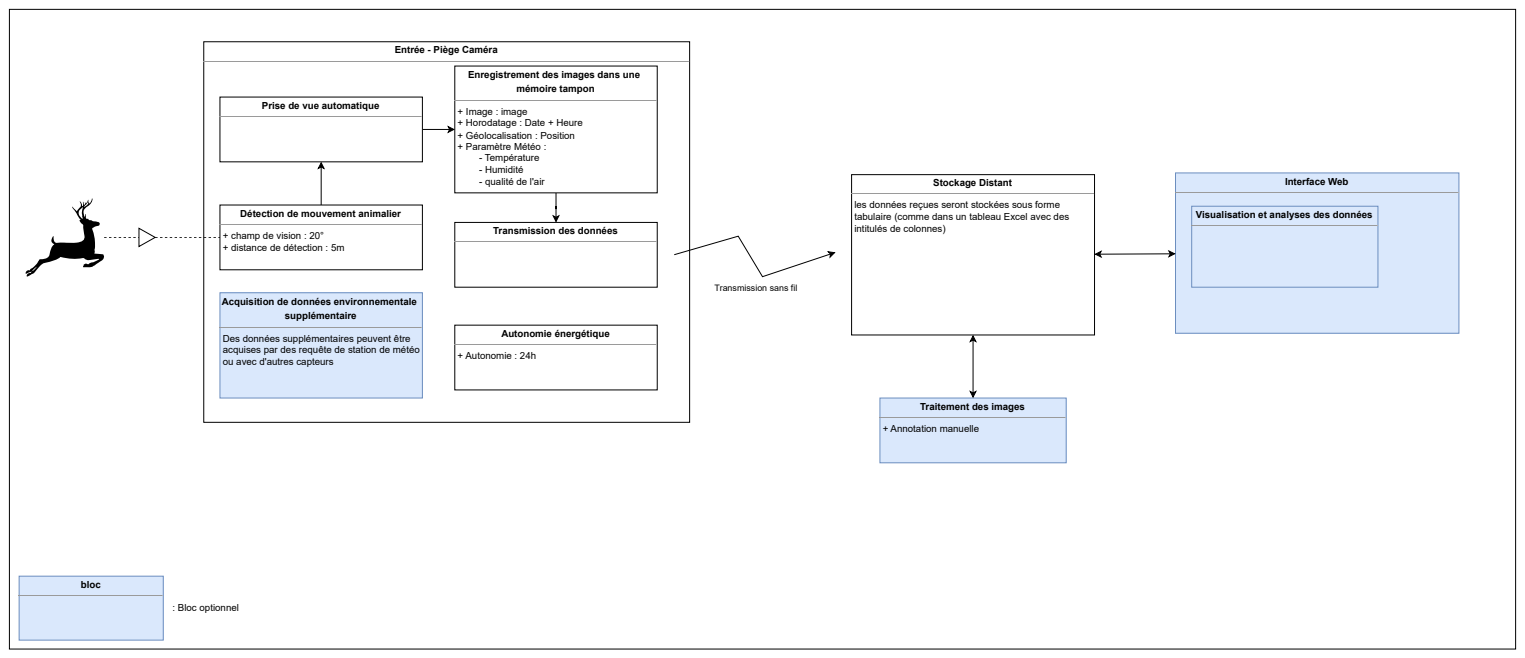
[picture p152: page 1]
Stockage Distant; mémoire tampon; Autonomie énergétique; + Autonomie : 24h; Interface Web; + Annotation manuelle; supplémentaire; bloc; : Bloc optionnel

Entrée - Piège Caméra

Enregistrement des images dans une

Prise de vue automatique

+ Image : image
+ Horodatage : Date + Heure
+ Géolocalisation : Position
+ Paramètre Météo :
- Température
- Humidité
- qualité de l'air

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

Détection de mouvement animalier

Visualisation et analyses des données

Transmission des données

+ champ de vision : 20°
+ distance de détection : 5m

Transmission sans fil

Acquisition de données environnementale

Des données supplémentaires peuvent être
acquises par des requête de station de météo
ou avec d'autres capteurs

Traitement des images
