Joris1306/Collecteur_de_donnees_animalieres/Stockage_Distant/DOCUMENT/rapport_documention/images/bete_a_corne.pdf

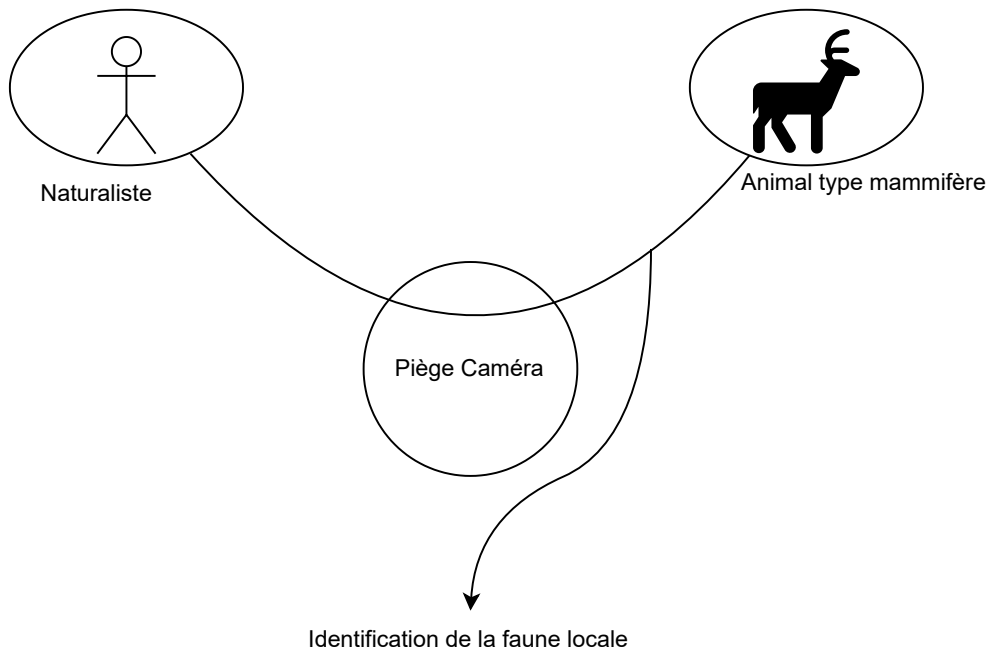
[picture p153: page 1]
Piège Caméra; Naturaliste; Animal type mammifère

Identification de la faune locale
