Joris1306/Collecteur_de_donnees_animalieres/ESP32-S3-N16R8/include/SDM.h

#ifndef SDM_H
#define SDM_H

#include <SPI.h>
#include <SD.h>
#include "CONFIG.h"

// Déclaration externe (pas de définition ici)
extern SPIClass hspi;

// Déclaration de la fonction
void initSD();

#endif // SDM_H
